schlizbaeda/FiatLanciaModules/Bilder/_Umbau02.jpg

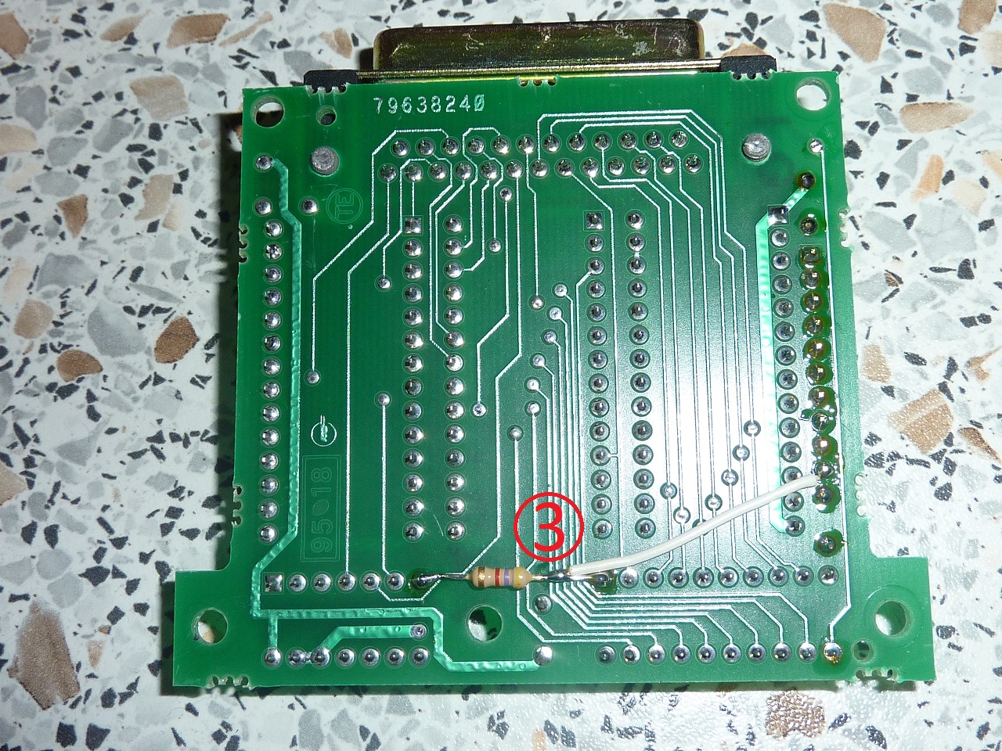
Bilder/_Umbau02.jpg
