schlizbaeda/FiatLanciaModules/Bilder/Adapter01.jpg

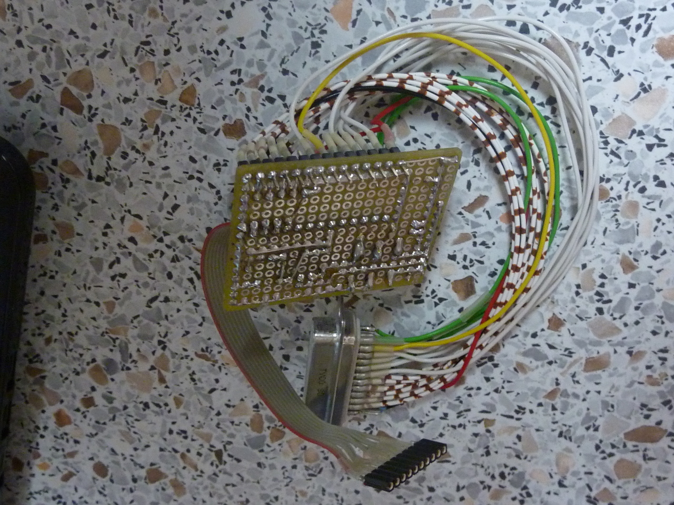
Bilder/Adapter01.jpg
