schlizbaeda/FiatLanciaModules/Bilder/Adapter02.jpg

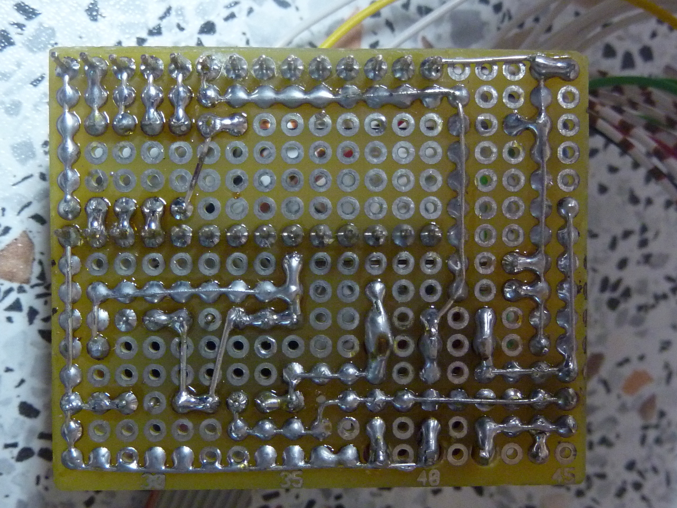
Bilder/Adapter02.jpg
