schlizbaeda/FiatLanciaModules/Bilder/Adapter.jpg

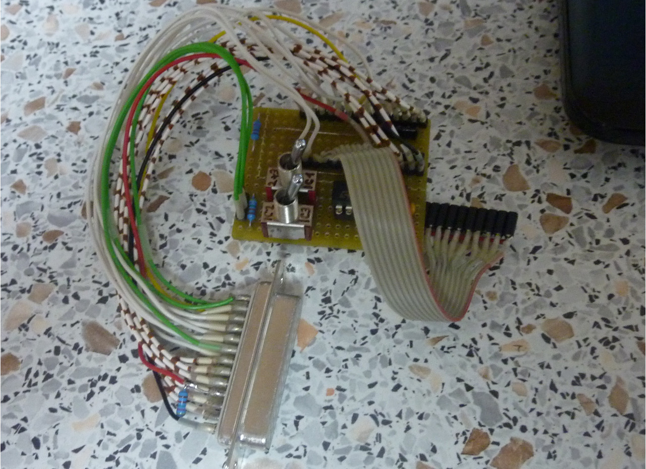
Bilder/Adapter.jpg
