schlizbaeda/FiatLanciaModules/Bilder/Modulanschluss.jpg

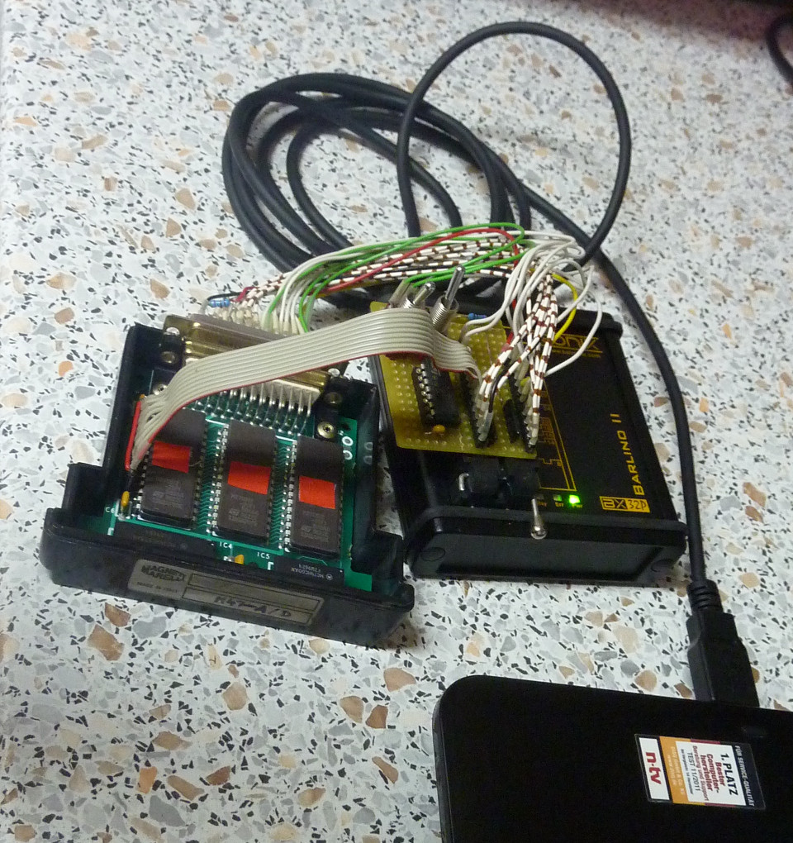
Bilder/Modulanschluss.jpg
