schlizbaeda/FiatLanciaModules/Bilder/Prog-Express_Auslesen_IC1_8kB.png

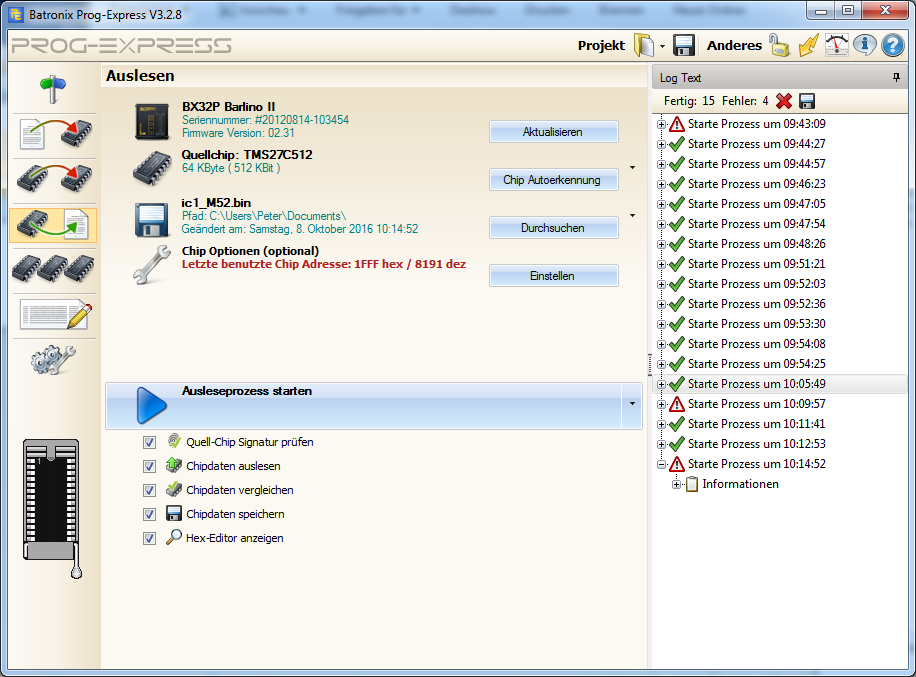
Bilder/Prog-Express_Auslesen_IC1_8kB.png
