schlizbaeda/FiatLanciaModules/Bilder/Prog-Express_Auslesen_IC1_8kB_Hexeditor.png

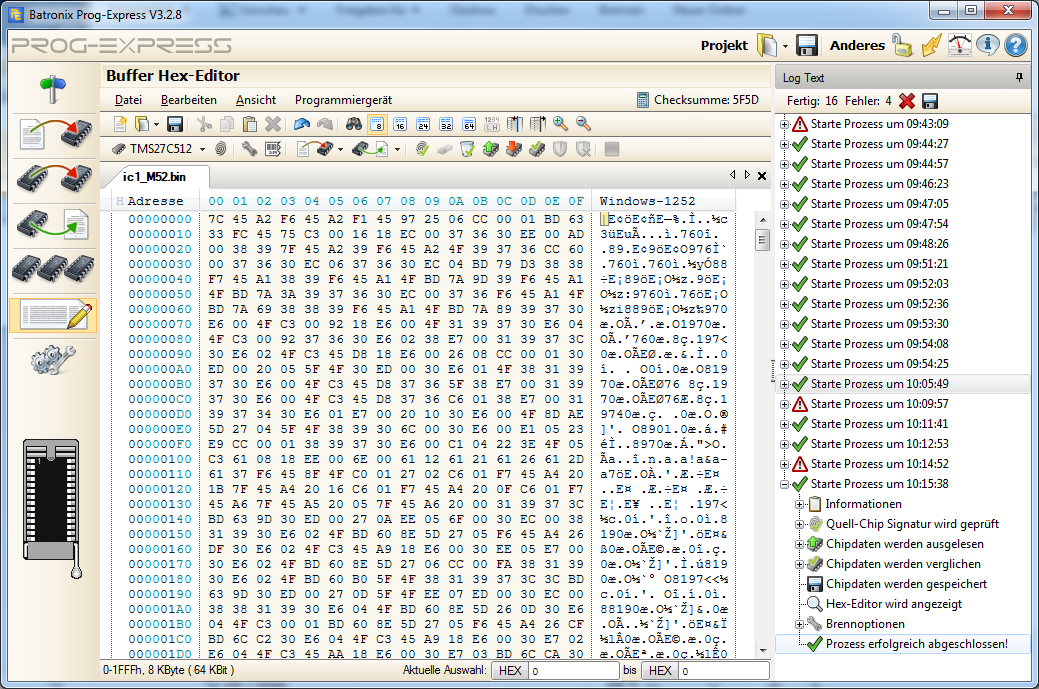
Bilder/Prog-Express_Auslesen_IC1_8kB_Hexeditor.png
