schlizbaeda/FiatLanciaModules/Bilder/Prog-Express_Auslesen_IC2.png

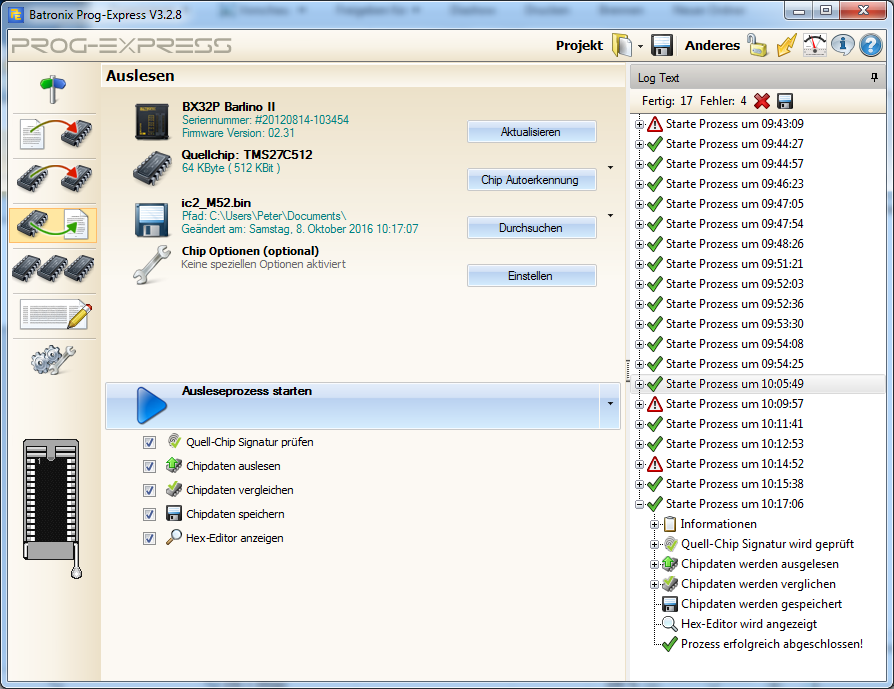
Bilder/Prog-Express_Auslesen_IC2.png
