schlizbaeda/FiatLanciaModules/Bilder/Prog-Express_ChipBrowser_01.png

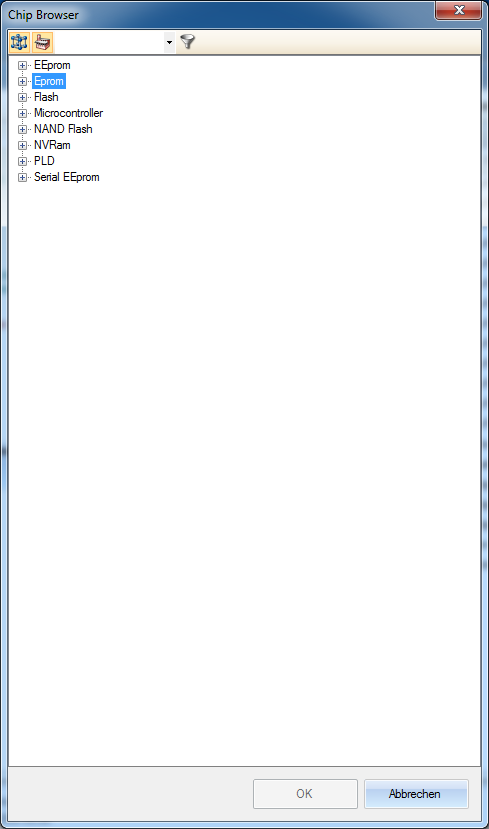
Bilder/Prog-Express_ChipBrowser_01.png
