schlizbaeda/FiatLanciaModules/Bilder/Prog-Express_ChipBrowser_02.png

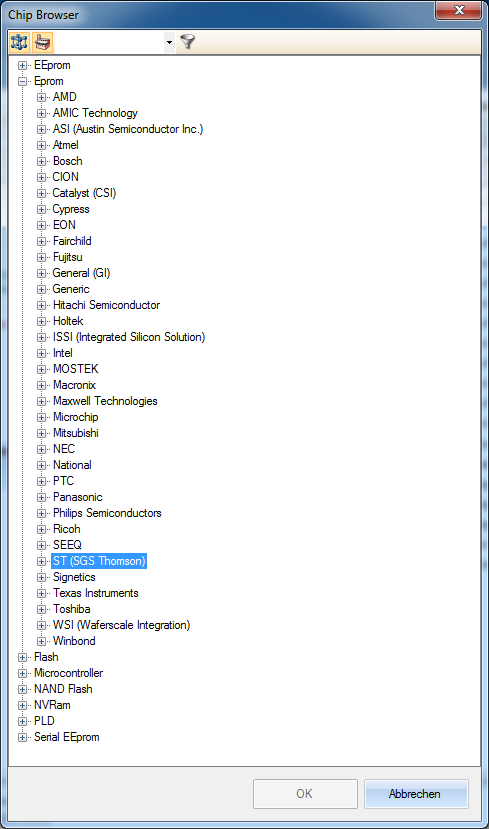
Bilder/Prog-Express_ChipBrowser_02.png
