schlizbaeda/FiatLanciaModules/Bilder/Prog-Express_ChipBrowser_03.png

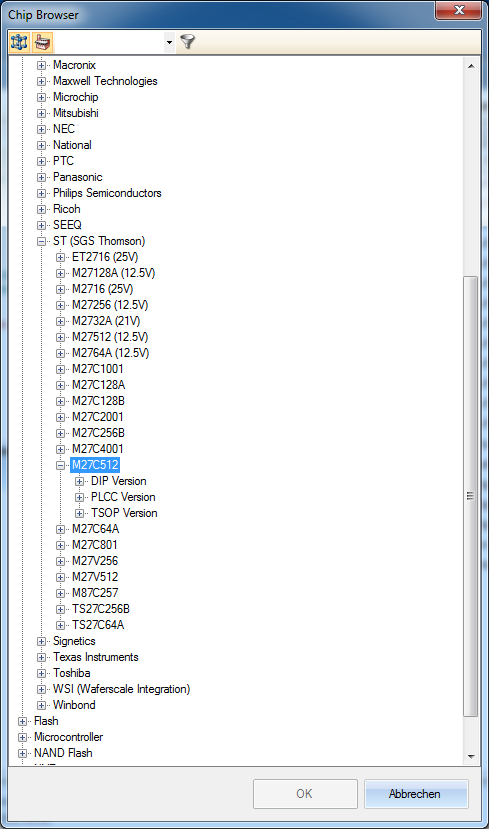
Bilder/Prog-Express_ChipBrowser_03.png
