schlizbaeda/FiatLanciaModules/Bilder/Prog-Express_ChipBrowser_03_alternativ_wegen_Chip-Signatur.png

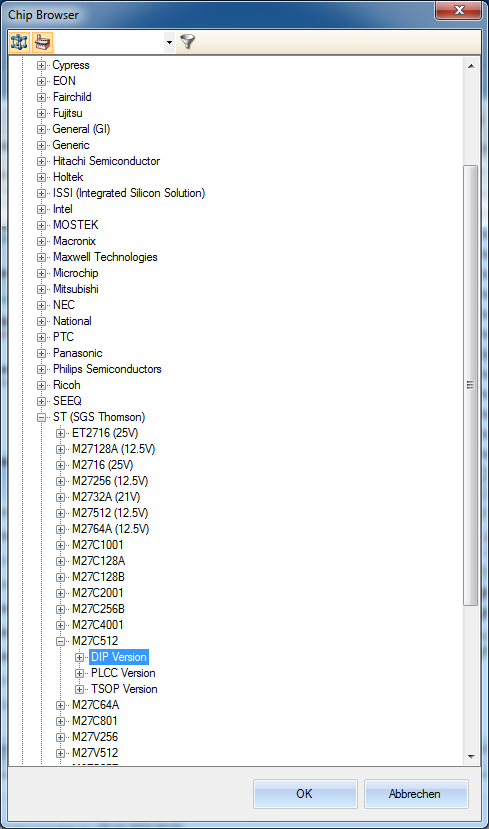
Bilder/Prog-Express_ChipBrowser_03_alternativ_wegen_Chip-Signatur.png
