schlizbaeda/FiatLanciaModules/Bilder/Prog-Express_ChipBrowser_04_Chip-Signatur_schlägt_fehl.png

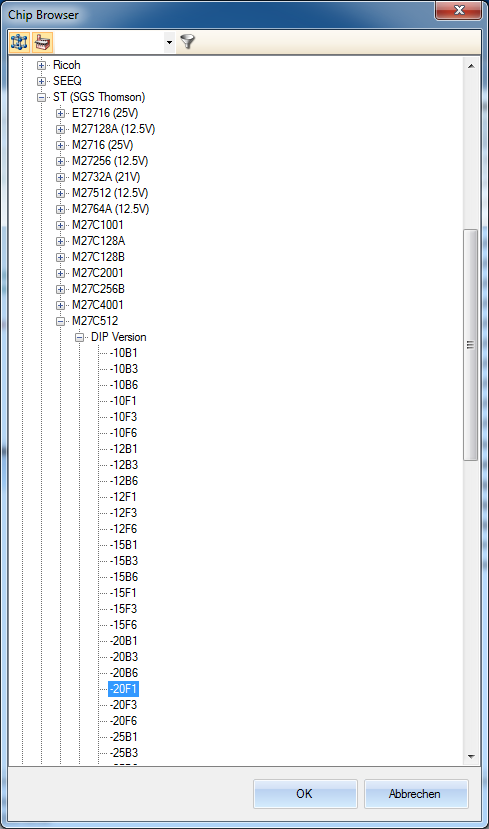
Bilder/Prog-Express_ChipBrowser_04_Chip-Signatur_schlägt_fehl.png
