schlizbaeda/FiatLanciaModules/Bilder/Prog-Express_Einstellungen_IC1.png

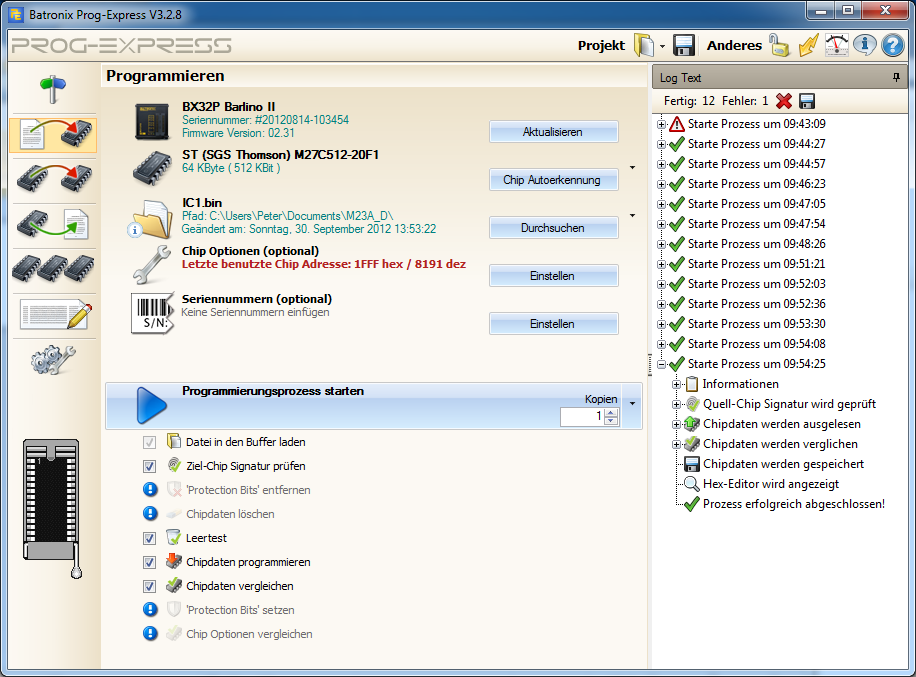
Bilder/Prog-Express_Einstellungen_IC1.png
