schlizbaeda/FiatLanciaModules/Bilder/Prog-Express_Einstellungen_IC2.png

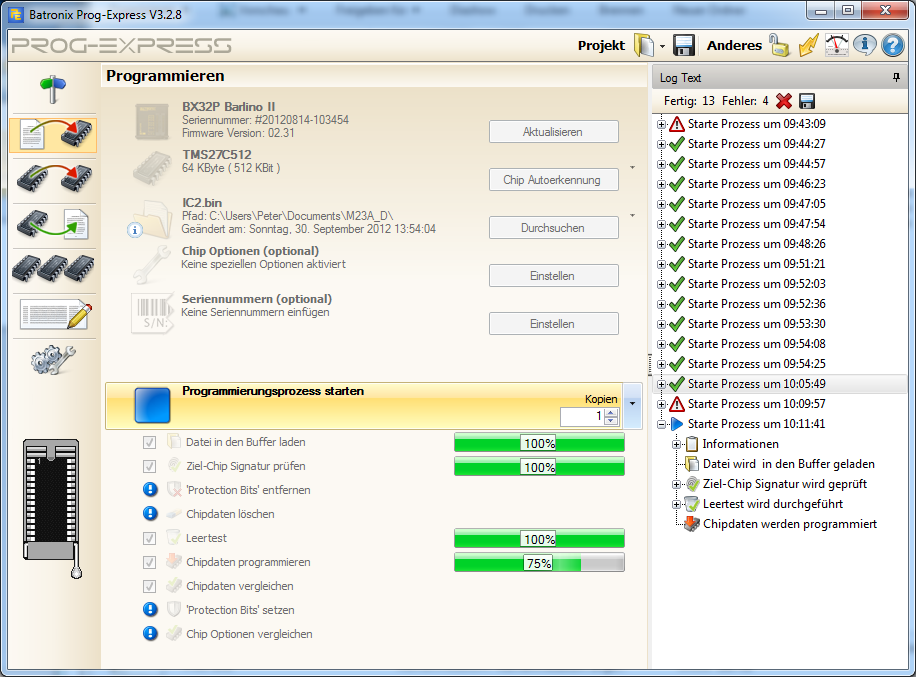
Bilder/Prog-Express_Einstellungen_IC2.png
