schlizbaeda/FiatLanciaModules/Bilder/Prog-Express_IC1_8kB.png

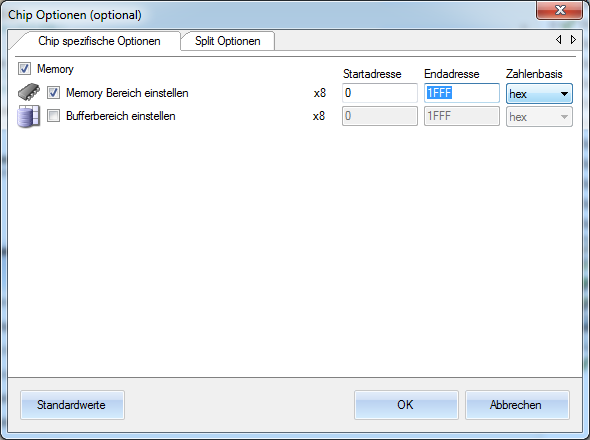
Bilder/Prog-Express_IC1_8kB.png
