schlizbaeda/FiatLanciaModules/Bilder/Programmiergeraet.jpg

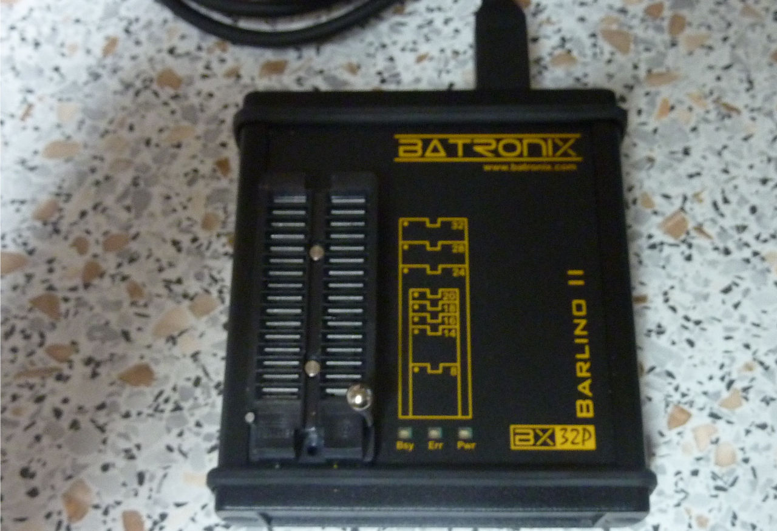
Bilder/Programmiergeraet.jpg
