schlizbaeda/FiatLanciaModules/Bilder/UV-Loeschgeraet.jpg

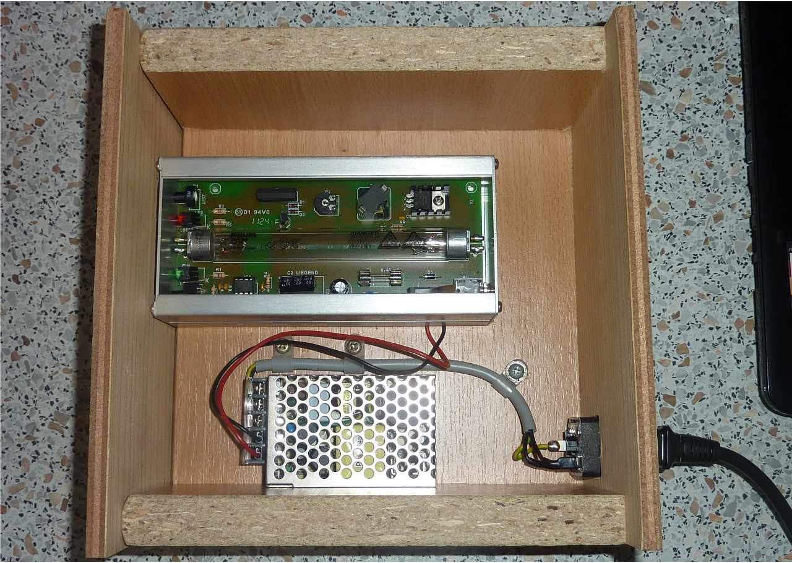
Bilder/UV-Loeschgeraet.jpg
